TahuTech/lumberjack-pcb/images/bom/c1-2.jpg

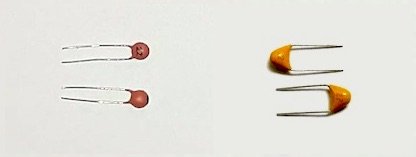
images/bom/c1-2.jpg
