TahuTech/lumberjack-pcb/images/bom/c4-5.jpg

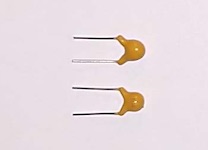
images/bom/c4-5.jpg
