TahuTech/lumberjack-pcb/images/bom/d61-62.jpg

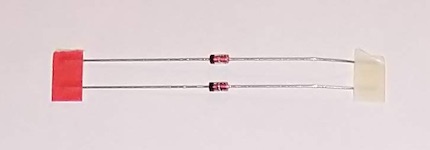
images/bom/d61-62.jpg
