TahuTech/lumberjack-pcb/images/bom/f1.jpg

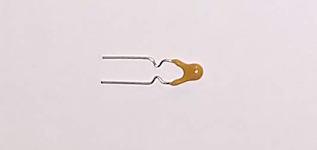
images/bom/f1.jpg
