TahuTech/lumberjack-pcb/images/bom/ic.jpg

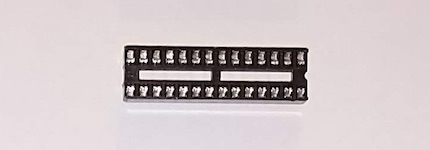
images/bom/ic.jpg
