TahuTech/lumberjack-pcb/images/bom/j1-mini.jpg

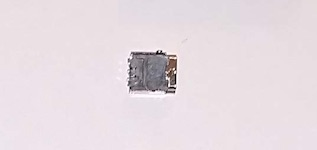
images/bom/j1-mini.jpg
