TahuTech/lumberjack-pcb/images/bom/j1-usbc.jpg

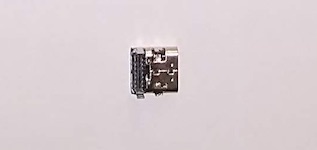
images/bom/j1-usbc.jpg
