TahuTech/lumberjack-pcb/images/bom/led1-2.jpg

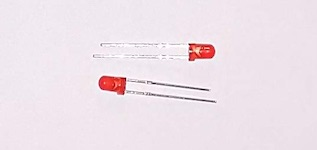
images/bom/led1-2.jpg
