TahuTech/lumberjack-pcb/images/bom/r1-7-8.jpg

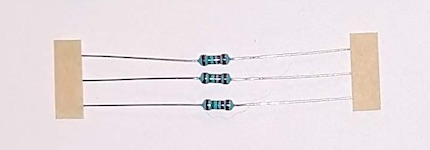
images/bom/r1-7-8.jpg
