TahuTech/lumberjack-pcb/images/bom/r2-3.jpg

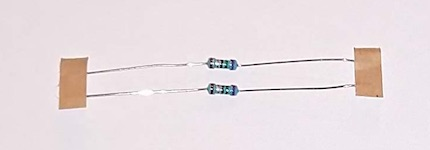
images/bom/r2-3.jpg
