TahuTech/lumberjack-pcb/images/bom/r5-6.jpg

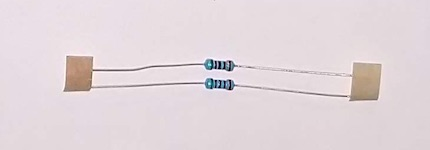
images/bom/r5-6.jpg
