TahuTech/lumberjack-pcb/images/bom/u1.jpg

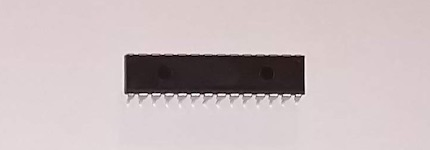
images/bom/u1.jpg
